astuder/dAISy/KiCad/dAISy BoosterPack/dAISy BoosterPack.png

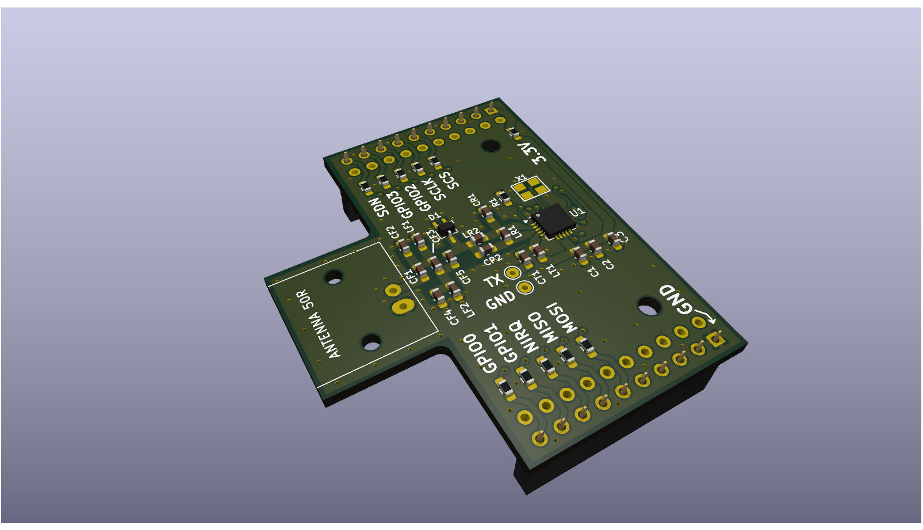
KiCad/dAISy BoosterPack/dAISy BoosterPack.png
