astuder/dAISy/KiCad/Si446x Breakout/OSHPark.png

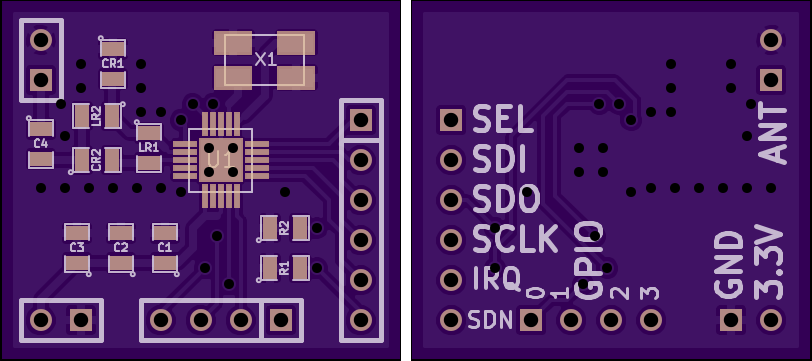
KiCad/Si446x Breakout/OSHPark.png
